dilshan/stm8s005-iot-devboard/firmware/net/drivers/enc28j60/enc28j60.h

//----------------------------------------------------------------------------
// ENC28J60 Eathernet driver for STM8 series MCUs.
// Copyright (C) 2021 Dilshan Jayakody.
//
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
#ifndef STM8_ENC28J60_ETH_DRV_H
#define STM8_ENC28J60_ETH_DRV_H

// MCU PortC pin mappings for ENC28J60 controller.
#define ENC28J60_CS_PIN 	4
#define ENC28J60_SCK_PIN	5
#define ENC28J60_MOSI_PIN	6
#define ENC28J60_MISO_PIN	7

// Start of RX buffer, (must be zero, Rev. B4 Errata point 5)
#define RXSTART_INIT        0x0000  

// End of RX buffer, room for 2 packets.
#define RXSTOP_INIT         0x0BFF  

// Start of TX buffer, room for 1 packet.
#define TXSTART_INIT        0x0C00  

// End of TX buffer.
#define TXSTOP_INIT         0x11FF  

// Start of scratch area
#define SCRATCH_START       0x1200 

// Past end of area, i.e. 3 Kb.
#define SCRATCH_LIMIT       0x2000 

// Addressing is in pages of 64 bytes.
#define SCRATCH_PAGE_SHIFT  6       
#define SCRATCH_PAGE_SIZE   (1 << SCRATCH_PAGE_SHIFT)
#define SCRATCH_PAGE_NUM    ((SCRATCH_LIMIT-SCRATCH_START) >> SCRATCH_PAGE_SHIFT)
#define SCRATCH_MAP_SIZE    (((SCRATCH_PAGE_NUM % 8) == 0) ? (SCRATCH_PAGE_NUM / 8) : (SCRATCH_PAGE_NUM/8+1))

// ENC28J60 Control Registers. (Based on initial work of Pascal Stang.)
// - Register address        (bits 0-4)
// - Bank number             (bits 5-6)
// - MAC/PHY indicator       (bit 7)
#define ADDR_MASK        0x1F
#define BANK_MASK        0x60
#define SPRD_MASK        0x80

// All-bank registers.
#define EIE              0x1B
#define EIR              0x1C
#define ESTAT            0x1D
#define ECON2            0x1E
#define ECON1            0x1F

// Bank 0 registers.
#define ERDPT           (0x00|0x00)
#define EWRPT           (0x02|0x00)
#define ETXST           (0x04|0x00)
#define ETXND           (0x06|0x00)
#define ERXST           (0x08|0x00)
#define ERXND           (0x0A|0x00)
#define ERXRDPT         (0x0C|0x00)
#define EDMAST          (0x10|0x00)
#define EDMAND          (0x12|0x00)
#define EDMACS          (0x16|0x00)

// Bank 1 registers.
#define EHT0             (0x00|0x20)
#define EHT1             (0x01|0x20)
#define EHT2             (0x02|0x20)
#define EHT3             (0x03|0x20)
#define EHT4             (0x04|0x20)
#define EHT5             (0x05|0x20)
#define EHT6             (0x06|0x20)
#define EHT7             (0x07|0x20)
#define EPMM0            (0x08|0x20)
#define EPMM1            (0x09|0x20)
#define EPMM2            (0x0A|0x20)
#define EPMM3            (0x0B|0x20)
#define EPMM4            (0x0C|0x20)
#define EPMM5            (0x0D|0x20)
#define EPMM6            (0x0E|0x20)
#define EPMM7            (0x0F|0x20)
#define EPMCS            (0x10|0x20) 
#define EWOLIE           (0x16|0x20)
#define EWOLIR           (0x17|0x20)
#define ERXFCON          (0x18|0x20)
#define EPKTCNT          (0x19|0x20)

// Bank 2 registers.
#define MACON1           (0x00|0x40|0x80)
#define MACON3           (0x02|0x40|0x80)
#define MACON4           (0x03|0x40|0x80)
#define MABBIPG          (0x04|0x40|0x80)
#define MAIPG            (0x06|0x40|0x80)
#define MACLCON1         (0x08|0x40|0x80)
#define MACLCON2         (0x09|0x40|0x80)
#define MAMXFL           (0x0A|0x40|0x80)
#define MAPHSUP          (0x0D|0x40|0x80)
#define MICON            (0x11|0x40|0x80)
#define MICMD            (0x12|0x40|0x80)
#define MIREGADR         (0x14|0x40|0x80)
#define MIWR             (0x16|0x40|0x80)
#define MIRD             (0x18|0x40|0x80)

// Bank 3 registers.
#define MAADR1           (0x00|0x60|0x80)
#define MAADR0           (0x01|0x60|0x80)
#define MAADR3           (0x02|0x60|0x80)
#define MAADR2           (0x03|0x60|0x80)
#define MAADR5           (0x04|0x60|0x80)
#define MAADR4           (0x05|0x60|0x80)
#define EBSTSD           (0x06|0x60)
#define EBSTCON          (0x07|0x60)
#define EBSTCS          (0x08|0x60)
#define MISTAT           (0x0A|0x60|0x80)
#define EREVID           (0x12|0x60)
#define ECOCON           (0x15|0x60)
#define EFLOCON          (0x17|0x60)
#define EPAUS           (0x18|0x60)

// ENC28J60 ERXFCON Register Bit Definitions.
#define ERXFCON_UCEN     0x80
#define ERXFCON_ANDOR    0x40
#define ERXFCON_CRCEN    0x20
#define ERXFCON_PMEN     0x10
#define ERXFCON_MPEN     0x08
#define ERXFCON_HTEN     0x04
#define ERXFCON_MCEN     0x02
#define ERXFCON_BCEN     0x01

// ENC28J60 EIE Register Bit Definitions.
#define EIE_INTIE        0x80
#define EIE_PKTIE        0x40
#define EIE_DMAIE        0x20
#define EIE_LINKIE       0x10
#define EIE_TXIE         0x08
#define EIE_WOLIE        0x04
#define EIE_TXERIE       0x02
#define EIE_RXERIE       0x01

// ENC28J60 EIR Register Bit Definitions.
#define EIR_PKTIF        0x40
#define EIR_DMAIF        0x20
#define EIR_LINKIF       0x10
#define EIR_TXIF         0x08
#define EIR_WOLIF        0x04
#define EIR_TXERIF       0x02
#define EIR_RXERIF       0x01

// ENC28J60 ESTAT Register Bit Definitions.
#define ESTAT_INT        0x80
#define ESTAT_LATECOL    0x10
#define ESTAT_RXBUSY     0x04
#define ESTAT_TXABRT     0x02
#define ESTAT_CLKRDY     0x01

// ENC28J60 ECON2 Register Bit Definitions.
#define ECON2_AUTOINC    0x80
#define ECON2_PKTDEC     0x40
#define ECON2_PWRSV      0x20
#define ECON2_VRPS       0x08

// ENC28J60 ECON1 Register Bit Definitions.
#define ECON1_TXRST      0x80
#define ECON1_RXRST      0x40
#define ECON1_DMAST      0x20
#define ECON1_CSUMEN     0x10
#define ECON1_TXRTS      0x08
#define ECON1_RXEN       0x04
#define ECON1_BSEL1      0x02
#define ECON1_BSEL0      0x01

// ENC28J60 MACON1 Register Bit Definitions.
#define MACON1_LOOPBK    0x10
#define MACON1_TXPAUS    0x08
#define MACON1_RXPAUS    0x04
#define MACON1_PASSALL   0x02
#define MACON1_MARXEN    0x01

// ENC28J60 MACON3 Register Bit Definitions.
#define MACON3_PADCFG2   0x80
#define MACON3_PADCFG1   0x40
#define MACON3_PADCFG0   0x20
#define MACON3_TXCRCEN   0x10
#define MACON3_PHDRLEN   0x08
#define MACON3_HFRMLEN   0x04
#define MACON3_FRMLNEN   0x02
#define MACON3_FULDPX    0x01

// ENC28J60 MICMD Register Bit Definitions.
#define MICMD_MIISCAN    0x02
#define MICMD_MIIRD      0x01

// ENC28J60 MISTAT Register Bit Definitions.
#define MISTAT_NVALID    0x04
#define MISTAT_SCAN      0x02
#define MISTAT_BUSY      0x01

// ENC28J60 EBSTCON Register Bit Definitions.
#define EBSTCON_PSV2     0x80
#define EBSTCON_PSV1     0x40
#define EBSTCON_PSV0     0x20
#define EBSTCON_PSEL     0x10
#define EBSTCON_TMSEL1   0x08
#define EBSTCON_TMSEL0   0x04
#define EBSTCON_TME      0x02
#define EBSTCON_BISTST    0x01

// PHY registers.
#define PHCON1           0x00
#define PHSTAT1          0x01
#define PHHID1           0x02
#define PHHID2           0x03
#define PHCON2           0x10
#define PHSTAT2          0x11
#define PHIE             0x12
#define PHIR             0x13
#define PHLCON           0x14

// ENC28J60 PHY PHCON1 Register Bit Definitions.
#define PHCON1_PRST      0x8000
#define PHCON1_PLOOPBK   0x4000
#define PHCON1_PPWRSV    0x0800
#define PHCON1_PDPXMD    0x0100

// ENC28J60 PHY PHSTAT1 Register Bit Definitions.
#define PHSTAT1_PFDPX    0x1000
#define PHSTAT1_PHDPX    0x0800
#define PHSTAT1_LLSTAT   0x0004
#define PHSTAT1_JBSTAT   0x0002

// ENC28J60 PHY PHCON2 Register Bit Definitions.
#define PHCON2_FRCLINK   0x4000
#define PHCON2_TXDIS     0x2000
#define PHCON2_JABBER    0x0400
#define PHCON2_HDLDIS    0x0100

// ENC28J60 Packet Control Byte Bit Definitions.
#define PKTCTRL_PHUGEEN  0x08
#define PKTCTRL_PPADEN   0x04
#define PKTCTRL_PCRCEN   0x02
#define PKTCTRL_POVERRIDE 0x01

// SPI operation codes.
#define ENC28J60_READ_CTRL_REG       0x00
#define ENC28J60_READ_BUF_MEM        0x3A
#define ENC28J60_WRITE_CTRL_REG      0x40
#define ENC28J60_WRITE_BUF_MEM       0x7A
#define ENC28J60_BIT_FIELD_SET       0x80
#define ENC28J60_BIT_FIELD_CLR       0xA0
#define ENC28J60_SOFT_RESET          0xFF

// Max frame length which the controller will accept:
// (note: maximum ethernet frame length would be 1518).
#define MAX_FRAMELEN      1500

unsigned char enc28j60Init(const unsigned char* macaddr);
unsigned char enc28j60IsLinkUp();

void enc28j60PacketSend(unsigned short len);
unsigned short enc28j60PacketReceive();

void enc28j60DisableBroadcast(unsigned char temporary);
void enc28j60EnableBroadcast(unsigned char temporary);

// Workaround for Errata 13.
#define ETHERCARD_RETRY_LATECOLLISIONS 0

// Enable pipelining of packet transmissions.
#define ETHERCARD_SEND_PIPELINING 0

#endif /* STM8_ENC28J60_ETH_DRV_H */
