dilshan/stm8s005-iot-devboard/firmware/include/stm8s001j3/flash.h

//----------------------------------------------------------------------------
// STM8S001J3 flash / EEPROM definitions for SDCC.
// Copyright (C) 2021 Dilshan Jayakody.
//
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
#ifndef STM8S001_FLASH_DEF_H
#define STM8S001_FLASH_DEF_H

#define FLASH_CR1_RESET_VALUE       ((unsigned char)0x00)       // CR1 reset value.
#define FLASH_CR2_RESET_VALUE       ((unsigned char)0x00)       // CR2 reset value.
#define FLASH_NCR2_RESET_VALUE      ((unsigned char)0xFF)       // NCR2 reset value.
#define FLASH_IAPSR_RESET_VALUE     ((unsigned char)0x40)       // IAPSR reset value.
#define FLASH_PUKR_RESET_VALUE      ((unsigned char)0x00)       // PUKR reset value.
#define FLASH_DUKR_RESET_VALUE      ((unsigned char)0x00)       // DUKR reset value.

#define FLASH_CR1_HALT              ((unsigned char)0x08)       // Standby in Halt mode mask.
#define FLASH_CR1_AHALT             ((unsigned char)0x04)       // Standby in Active Halt mode mask.
#define FLASH_CR1_IE                ((unsigned char)0x02)       // Flash Interrupt enable mask.
#define FLASH_CR1_FIX               ((unsigned char)0x01)       // Fix programming time mask.

#define FLASH_CR2_OPT               ((unsigned char)0x80)       // Select option byte mask.
#define FLASH_CR2_WPRG              ((unsigned char)0x40)       // Word Programming mask.
#define FLASH_CR2_ERASE             ((unsigned char)0x20)       // Erase block mask.
#define FLASH_CR2_FPRG              ((unsigned char)0x10)       // Fast programming mode mask.
#define FLASH_CR2_PRG               ((unsigned char)0x01)       // Program block mask.
 
#define FLASH_NCR2_NOPT             ((unsigned char)0x80)       // Select option byte mask.
#define FLASH_NCR2_NWPRG            ((unsigned char)0x40)       // Word Programming mask.
#define FLASH_NCR2_NERASE           ((unsigned char)0x20)       // Erase block mask.
#define FLASH_NCR2_NFPRG            ((unsigned char)0x10)       // Fast programming mode mask.
#define FLASH_NCR2_NPRG             ((unsigned char)0x01)       // Program block mask.

#define FLASH_IAPSR_HVOFF           ((unsigned char)0x40)       // End of high voltage flag mask.
#define FLASH_IAPSR_DUL             ((unsigned char)0x08)       // Data EEPROM unlocked flag mask.
#define FLASH_IAPSR_EOP             ((unsigned char)0x04)       // End of operation flag mask.
#define FLASH_IAPSR_PUL             ((unsigned char)0x02)       // Flash Program memory unlocked flag mask.
#define FLASH_IAPSR_WR_PG_DIS       ((unsigned char)0x01)       // Write attempted to protected page mask.

#endif /* STM8S001_FLASH_DEF_H */
