dilshan/stm8s005-iot-devboard/firmware/include/stm8s005c6/uart2def.h

//----------------------------------------------------------------------------
// STM8S005C6, STM8S005K6 UART2 definitions for SDCC.
// Copyright (C) 2021 Dilshan Jayakody.
//
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
#ifndef STM8S005_UART2_DEF_H
#define STM8S005_UART2_DEF_H

#define UART2_SR_RESET_VALUE    ((unsigned char)0xC0)   // SR reset value.
#define UART2_BRR1_RESET_VALUE  ((unsigned char)0x00)   // BRR1 reset value.
#define UART2_BRR2_RESET_VALUE  ((unsigned char)0x00)   // BRR2 reset value.
#define UART2_CR1_RESET_VALUE   ((unsigned char)0x00)   // CR1 reset value.
#define UART2_CR2_RESET_VALUE   ((unsigned char)0x00)   // CR2 reset value.
#define UART2_CR3_RESET_VALUE   ((unsigned char)0x00)   // CR3 reset value.
#define UART2_CR4_RESET_VALUE   ((unsigned char)0x00)   // CR4 reset value.
#define UART2_CR5_RESET_VALUE   ((unsigned char)0x00)   // CR5 reset value.
#define UART2_GTR_RESET_VALUE   ((unsigned char)0x00)   // GTR reset value.
#define UART2_PSCR_RESET_VALUE  ((unsigned char)0x00)   // PSCR reset value.

#define UART2_SR_TXE    ((unsigned char)0x80)   // Transmit Data Register Empty mask.
#define UART2_SR_TC     ((unsigned char)0x40)   // Transmission Complete mask.
#define UART2_SR_RXNE   ((unsigned char)0x20)   // Read Data Register Not Empty mask.
#define UART2_SR_IDLE   ((unsigned char)0x10)   // IDLE line detected mask.
#define UART2_SR_OR     ((unsigned char)0x08)   // OverRun error mask.
#define UART2_SR_NF     ((unsigned char)0x04)   // Noise Flag mask.
#define UART2_SR_FE     ((unsigned char)0x02)   // Framing Error mask.
#define UART2_SR_PE     ((unsigned char)0x01)   // Parity Error mask.

#define UART2_CR1_R8        ((unsigned char)0x80)   // Receive Data bit 8.
#define UART2_CR1_T8        ((unsigned char)0x40)   // Transmit data bit 8.
#define UART2_CR1_UARTD     ((unsigned char)0x20)   // UART1 Disable (for low power consumption).
#define UART2_CR1_M         ((unsigned char)0x10)   // Word length mask.
#define UART2_CR1_WAKE      ((unsigned char)0x08)   // Wake-up method mask.
#define UART2_CR1_PCEN      ((unsigned char)0x04)   // Parity Control Enable mask.
#define UART2_CR1_PS        ((unsigned char)0x02)   // UART1 Parity Selection.
#define UART2_CR1_PIEN      ((unsigned char)0x01)   // UART1 Parity Interrupt Enable mask.

#define UART2_CR2_TIEN      ((unsigned char)0x80)   // Transmitter Interrupt Enable mask.
#define UART2_CR2_TCIEN     ((unsigned char)0x40)   // Transmission Complete Interrupt Enable mask.
#define UART2_CR2_RIEN      ((unsigned char)0x20)   // Receiver Interrupt Enable mask.
#define UART2_CR2_ILIEN     ((unsigned char)0x10)   // IDLE Line Interrupt Enable mask.
#define UART2_CR2_TEN       ((unsigned char)0x08)   // Transmitter Enable mask.
#define UART2_CR2_REN       ((unsigned char)0x04)   // Receiver Enable mask.
#define UART2_CR2_RWU       ((unsigned char)0x02)   // Receiver Wake-Up mask.
#define UART2_CR2_SBK       ((unsigned char)0x01)   // Send Break mask.

#define UART2_CR3_LINEN     ((unsigned char)0x40)   // Alternate Function output mask.
#define UART2_CR3_STOP      ((unsigned char)0x30)   // STOP bits [1:0] mask.
#define UART2_CR3_CKEN      ((unsigned char)0x08)   // Clock Enable mask.
#define UART2_CR3_CPOL      ((unsigned char)0x04)   // Clock Polarity mask.
#define UART2_CR3_CPHA      ((unsigned char)0x02)   // Clock Phase mask.
#define UART2_CR3_LBCL      ((unsigned char)0x01)   // Last Bit Clock pulse mask.

#define UART2_CR4_LBDIEN    ((unsigned char)0x40)   // LIN Break Detection Interrupt Enable mask.
#define UART2_CR4_LBDL      ((unsigned char)0x20)   // LIN Break Detection Length mask.
#define UART2_CR4_LBDF      ((unsigned char)0x10)   // LIN Break Detection Flag mask.
#define UART2_CR4_ADD       ((unsigned char)0x0F)   // Address of the UART1 node mask.

#define UART2_CR5_SCEN      ((unsigned char)0x20)   // Smart Card Enable mask.
#define UART2_CR5_NACK      ((unsigned char)0x10)   // Smart Card Nack Enable mask.
#define UART2_CR5_HDSEL     ((unsigned char)0x08)   // Half-Duplex Selection mask.
#define UART2_CR5_IRLP      ((unsigned char)0x04)   // Irda Low Power Selection mask.
#define UART2_CR5_IREN      ((unsigned char)0x02)   // Irda Enable mask.

#define UART2_CR6_LDUM      ((unsigned char)0x80)   // LIN Divider Update Method.
#define UART2_CR6_LSLV      ((unsigned char)0x20)   // LIN Slave Enable.
#define UART2_CR6_LASE      ((unsigned char)0x10)   // LIN Auto synchronization Enable.
#define UART2_CR6_LHDIEN    ((unsigned char)0x04)   // LIN Header Detection Interrupt Enable.
#define UART2_CR6_LHDF      ((unsigned char)0x02)   // LIN Header Detection Flag.
#define UART2_CR6_LSF       ((unsigned char)0x01)   // LIN Synch Field.

#endif /* STM8S005_UART2_DEF_H */
