dilshan/stm8s005-iot-devboard/firmware/include/stm8-uart.h

//----------------------------------------------------------------------------
// STM8S UART library for serial communication.
// Copyright (C) 2021 Dilshan Jayakody.
//
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
#ifndef HARDWARE_UART1_H
#define HARDWARE_UART1_H

#include "stm8-common.h"
#include "../include/stm8.h"

// UART module number to use with this library. Set 1 for UART1 or 2 for UART2.
// DO NOT provide UART3 and above support for this library because those UART
// units are assigned for special functions in firmware.
#define UART_MODULE 2

#ifndef UART_MODULE
#warning "UART module ID is not specified. Use UART1 for serial communication library."
#define UART_MODULE 1
#endif

#if(UART_MODULE == 1)
#define UART_SR         UART1_SR
#define UART_SR_RXNE    UART1_SR_RXNE
#define UART_BRR2       UART1_BRR2
#define UART_BRR1       UART1_BRR1
#define UART_CR2        UART1_CR2
#define UART_CR2_TEN    UART1_CR2_TEN
#define UART_CR2_REN    UART1_CR2_REN
#define UART_DR         UART1_DR
#define UART_SR_TC      UART1_SR_TC
#else
#define UART_SR         UART2_SR
#define UART_SR_RXNE    UART2_SR_RXNE
#define UART_BRR2       UART2_BRR2
#define UART_BRR1       UART2_BRR1
#define UART_CR2        UART2_CR2
#define UART_CR2_TEN    UART2_CR2_TEN
#define UART_CR2_REN    UART2_CR2_REN
#define UART_DR         UART2_DR
#define UART_SR_TC      UART2_SR_TC
#endif

// BAUD rate need to define in project source or at makefile(s).
#ifndef BAUD_RATE1  
#warning "BAUD rate 1 is not defined. Use standard BAUD rate 9600 (CLK = 2MHz)."
#define BAUD_RATE1 0x0D
#endif

#ifndef BAUD_RATE2  
#warning "BAUD rate 2 is not defined. Use standard BAUD rate 9600 (CLK = 2MHz)."
#define BAUD_RATE2 0x01
#endif

void uartInit();
void uartWrite(unsigned char data);
unsigned char uartRead();

#define uartGetByte() (UART1_DR)

static inline unsigned char uartDataAvailable()
{
    return (UART_SR & UART_SR_RXNE);
}

#endif /* HARDWARE_UART1_H */
